GDWoody/Pixel-Controllers/bbb_8_push/jlcpcb/README.md

# BBB 8v1 SMD Push Fit Controller

## Copyright and Disclaimer
Copyright: GDWoody

This documentation describes Open Hardware and is licensed under the CERN Open Hardware License Version 2 - Strongly Reciprocal. (CERN-OHL-S)

You may redistribute and modify this documentation under the terms of the CERN OHL-S-v2 (https://ohwr.org/cern_ohl_s_v2.txt). This documentation is distributed WITHOUT ANY EXPRESS OR IMPLIED WARRANTY, INCLUDING OF MERCHANTABILITY, SATISFACTORY QUALITY AND FITNESS FOR A PARTICULAR PURPOSE. Please see the CERN OHL v2-S for applicable conditions

Under CERN OHL-S-v2, derivative work must be publicly released as defined in subsection 3.3

---
## BBB 8v1 SMD Push Fit Controller PCB's and Part Ordering
Following the instructions below your boards will arrive with only the SMD components fitted. To complete them you will also need to get and fit the 'Additional Components'.  

## To order BBB 8v1 SMD Push Fit PCBs From JLCPCB:

* Download the  [**Gerber_BBB_8v1_SMD_PCB_Push.zip**](https://github.com/GDWoody/Pixel-Controllers/blob/main/bbb_8_push/jlcpcb/gerber/Gerber_BBB_8v1_SMD_PCB_Push.zip) file in the jlcpcb\gerber folder.

* Download the  [**BOM_BBB_8v1_SMD_Push.xlsx**](https://github.com/GDWoody/Pixel-Controllers/blob/main/bbb_8_push/jlcpcb/assembly/BOM_BBB_8v1_SMD_Push.xlsx) file in the jlcpcb\assembly folder.

* Download the  [**CPL_BBB_8v1_SMD_PCB_Push.xlsx**](https://github.com/GDWoody/Pixel-Controllers/blob/main/bbb_8_push/jlcpcb/assembly/CPL_BBB_8v1_SMD_PCB_Push.xlsx) file in the jlcpcb\assembly folder.

*  Goto [**jlcpcb.com**](https://jlcpcb.com), sign in or make a new account, select Instant Quote and Upload the the Gerber_BBB_8v1_SMD_PCB_Push.zip file.

* The default settings should be ok. However you can choose 'PCB Color' and change 'Remove Order Number' to 'Specify a location'.

* Enable the SMD service, 'BOM_BBB_8v1_SMD_Push.xlsx' is the BOM file and 'CPL_BBB_8v1_SMD_PCB_Push.xlsx' is the CPL file.

* [**See here for detailed PCB ordering instructions for JLCPCB**](https://github.com/GDWoody/Pixel-Controllers/blob/main/JLC_PCB.md)

## To order Additional Required Parts from LCSC

* Download the [**BOM_BBB_8v1_SMD_Push_other_parts.xlsx**](https://github.com/GDWoody/Pixel-Controllers/blob/main/bbb_8_push/lcsc/BOM_BBB_8v1_SMD_Push_other_parts.xlsx) file in the lcsc folder.

* Goto [**lcsc.com**](https://lcsc.com), sign in or make a new account and select 'BOM Tool' and upload the BOM_BBB_16v2_SMD_PCB_Other_Parts.xlsx file.

* [**See here for detailed Parts ordering instructions for LCSC**](https://github.com/GDWoody/Pixel-Controllers/blob/main/LCSC.md)

## [**DIY Instructions for a BBB 8v1 SMD Push Fit Controller build**](https://github.com/GDWoody/Pixel-Controllers/blob/main/bbb_8_push/BBB_8v1_Push_DIY.md)

## [**Interactive Bom**](https://gdwoody.github.io/bbb_8_push/BOM_BBB_8v1_SMD_push_ibom.html)

## Additional Components Required

* A BeagleBone Black, BeagleBone Black Wireless, BeagleBone Green, or SanCloud BeagleBone enhanced 

* A SSD1306 128x64 OLED Display
