GDWoody/Pixel-Controllers/bbb_4/image/BBB_4v1_SMD_only.png

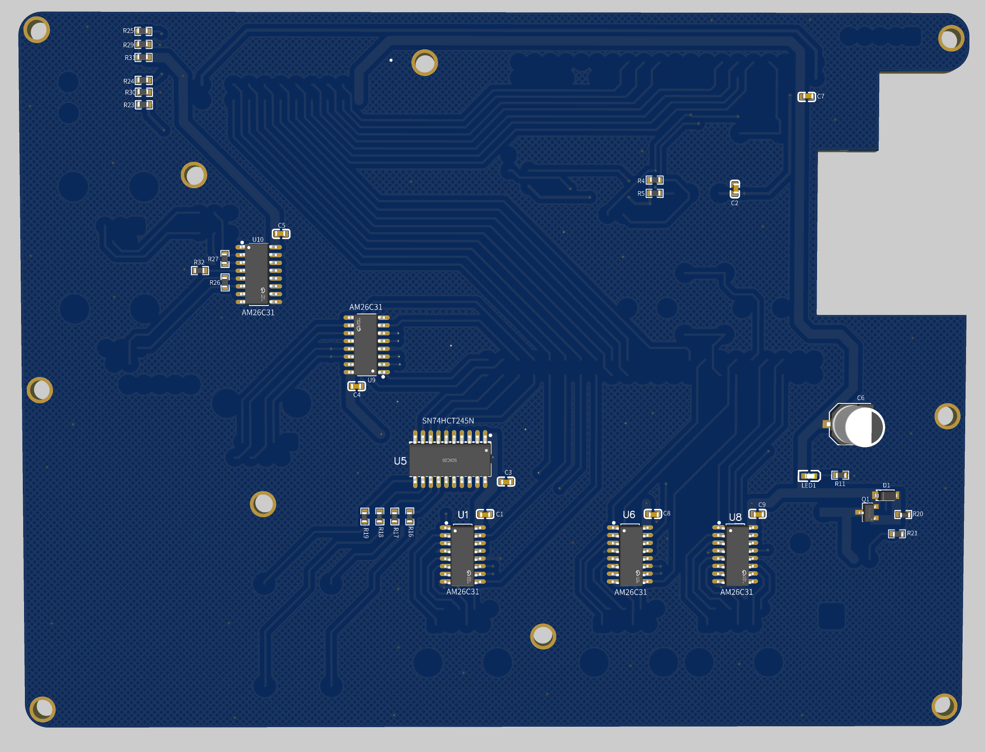
bbb_4/image/BBB_4v1_SMD_only.png
