GDWoody/Pixel-Controllers/bbb_4_push/image/BBB_4v1_Push_SMD_only.png

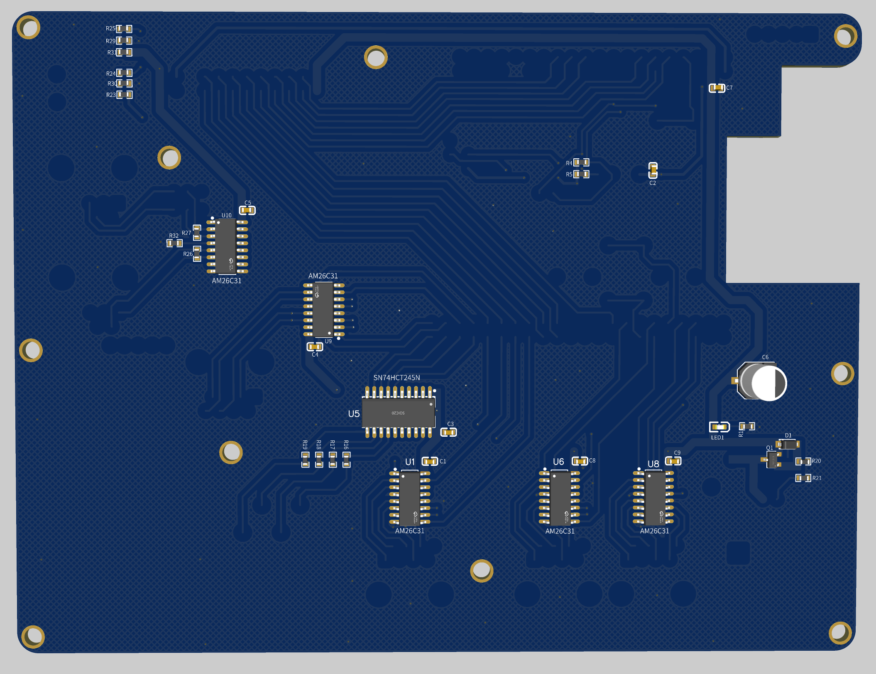
bbb_4_push/image/BBB_4v1_Push_SMD_only.png
