GDWoody/Pixel-Controllers/bbb_8/image/BBB_8v1_no_SMD.png

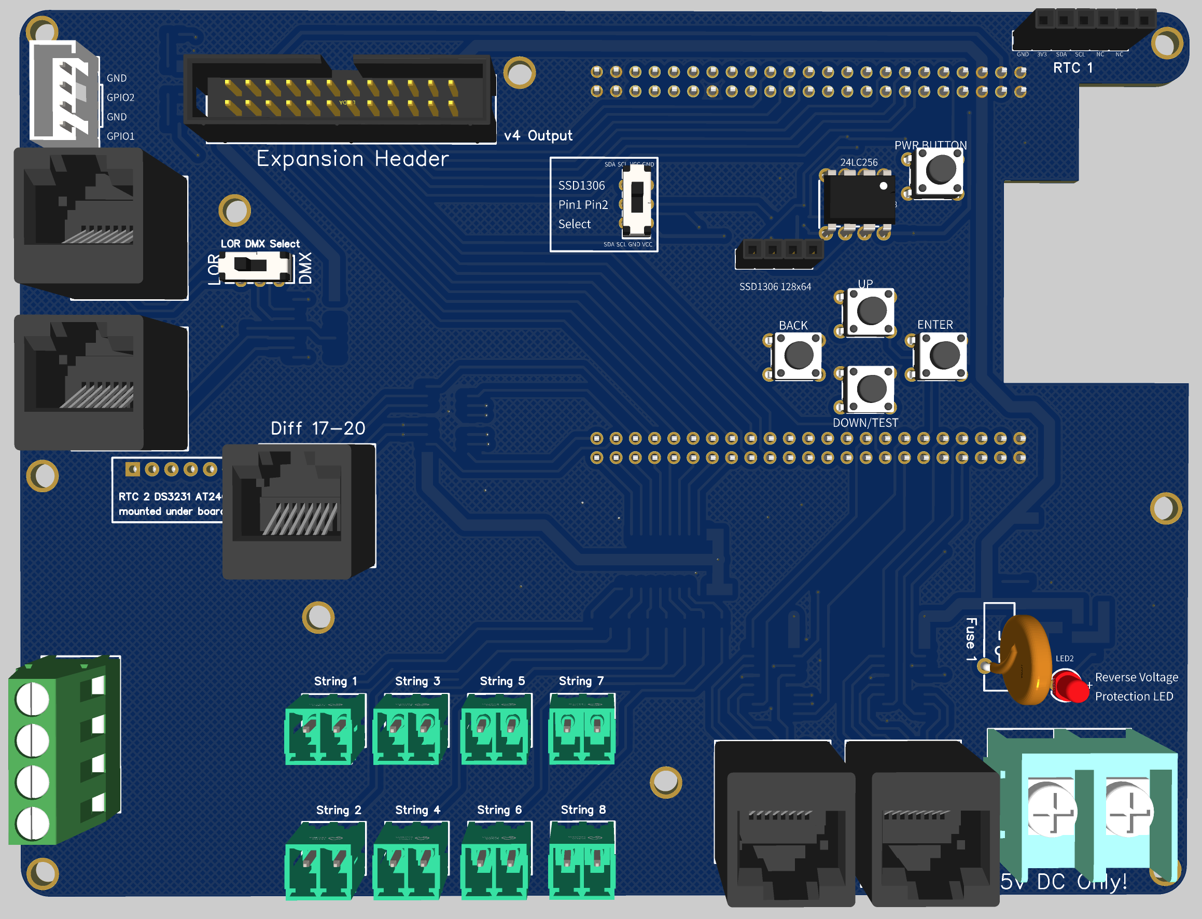
bbb_8/image/BBB_8v1_no_SMD.png
