GDWoody/Pixel-Controllers/bbb_8/image/BBB_8v1_SMD_only.png

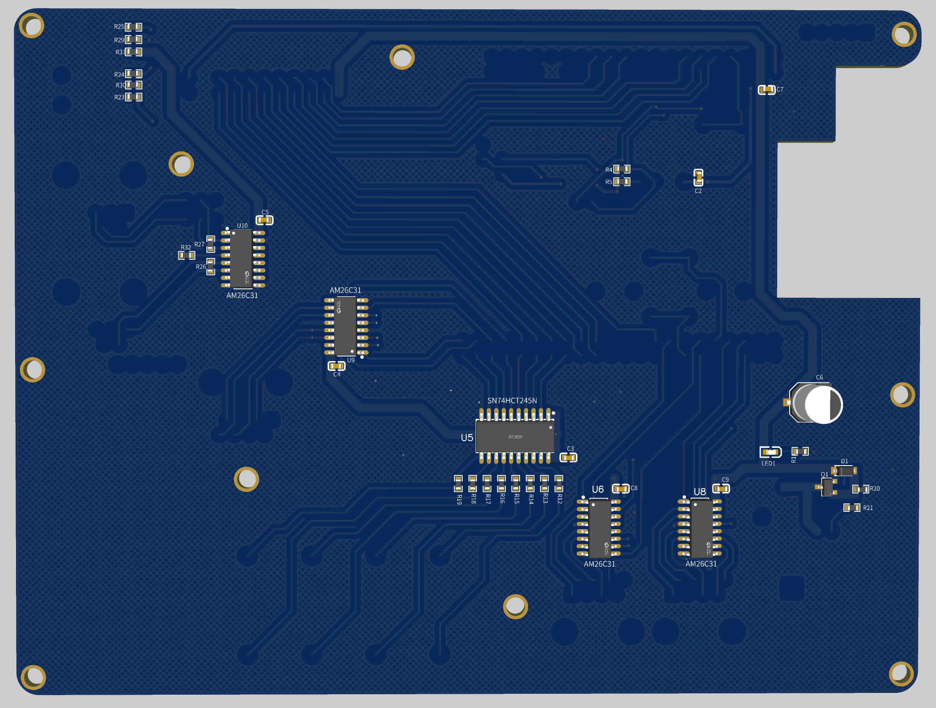
bbb_8/image/BBB_8v1_SMD_only.png
