GDWoody/Pixel-Controllers/bbb_8_push/image/BBB_8v1_Push_Under.png

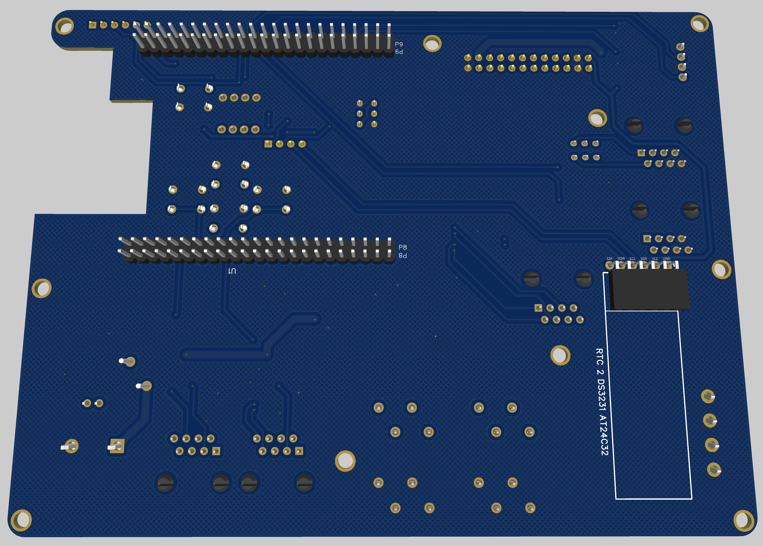
bbb_8_push/image/BBB_8v1_Push_Under.png
