GDWoody/Pixel-Controllers/bbb_16_push/image/BBB_16v2_Push_Other.png

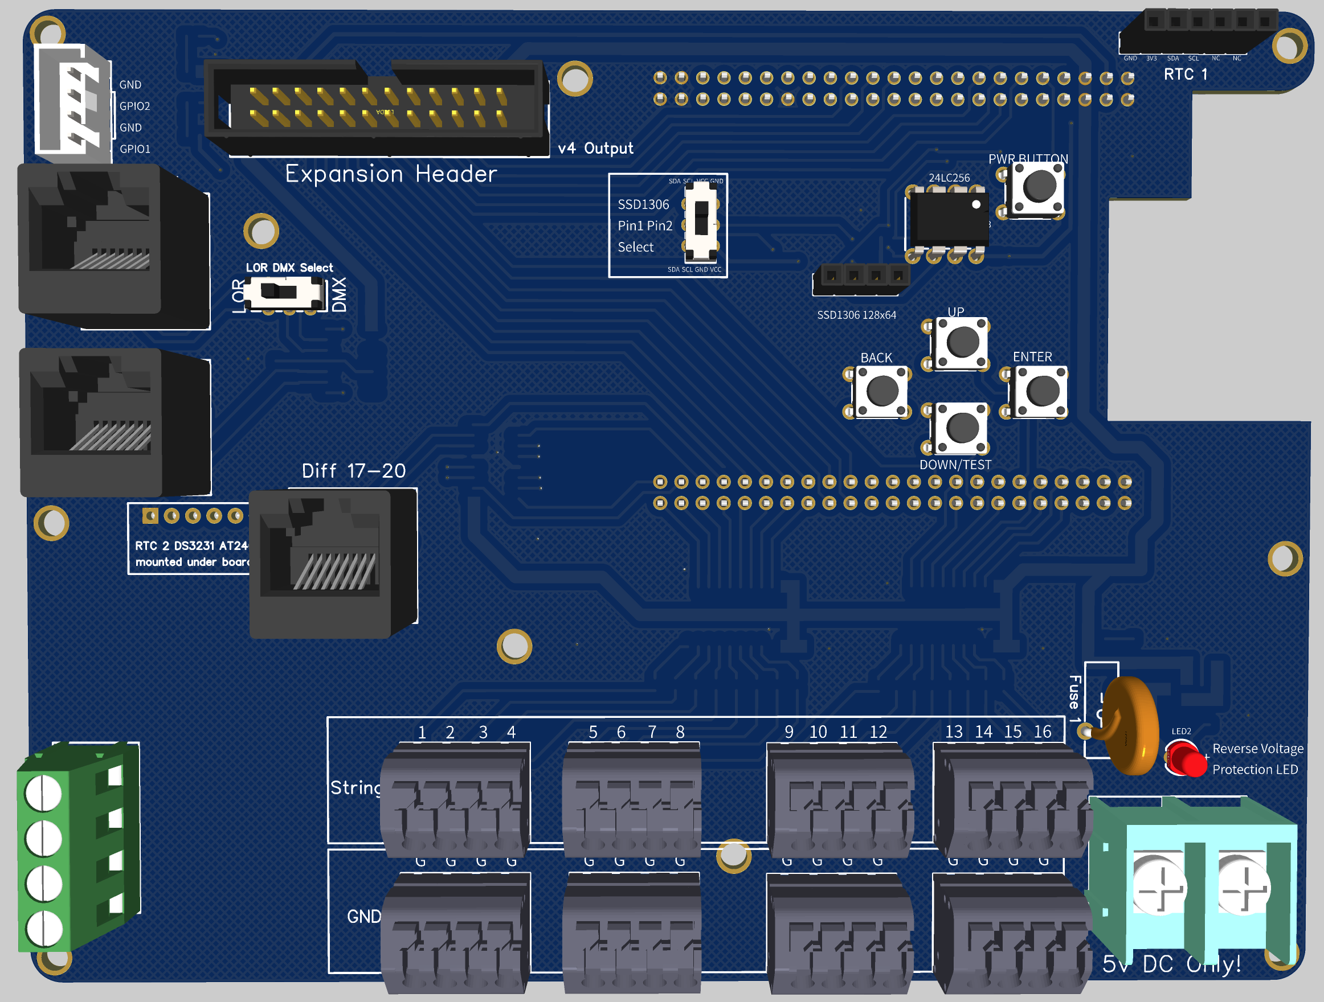
bbb_16_push/image/BBB_16v2_Push_Other.png
