GDWoody/Pixel-Controllers/bbb_16_push/image/BBB_16v2_Push_Under.png

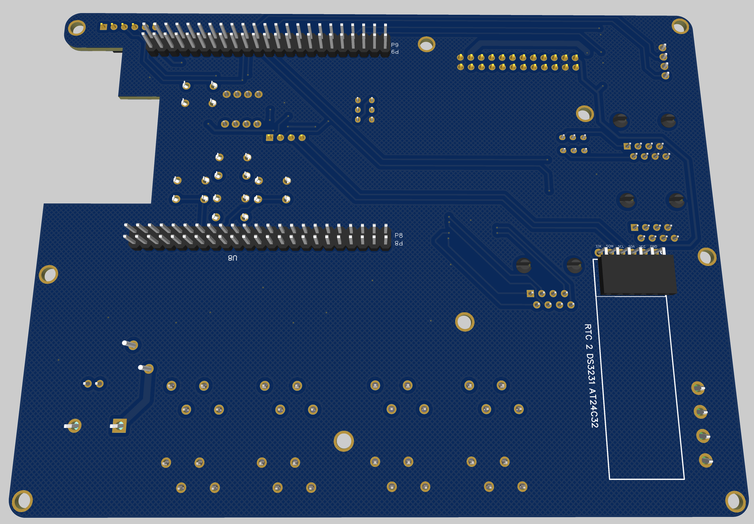
bbb_16_push/image/BBB_16v2_Push_Under.png
