GDWoody/Pixel-Controllers/bbb_all_diff/image/BBB_All_Diff_complete.png

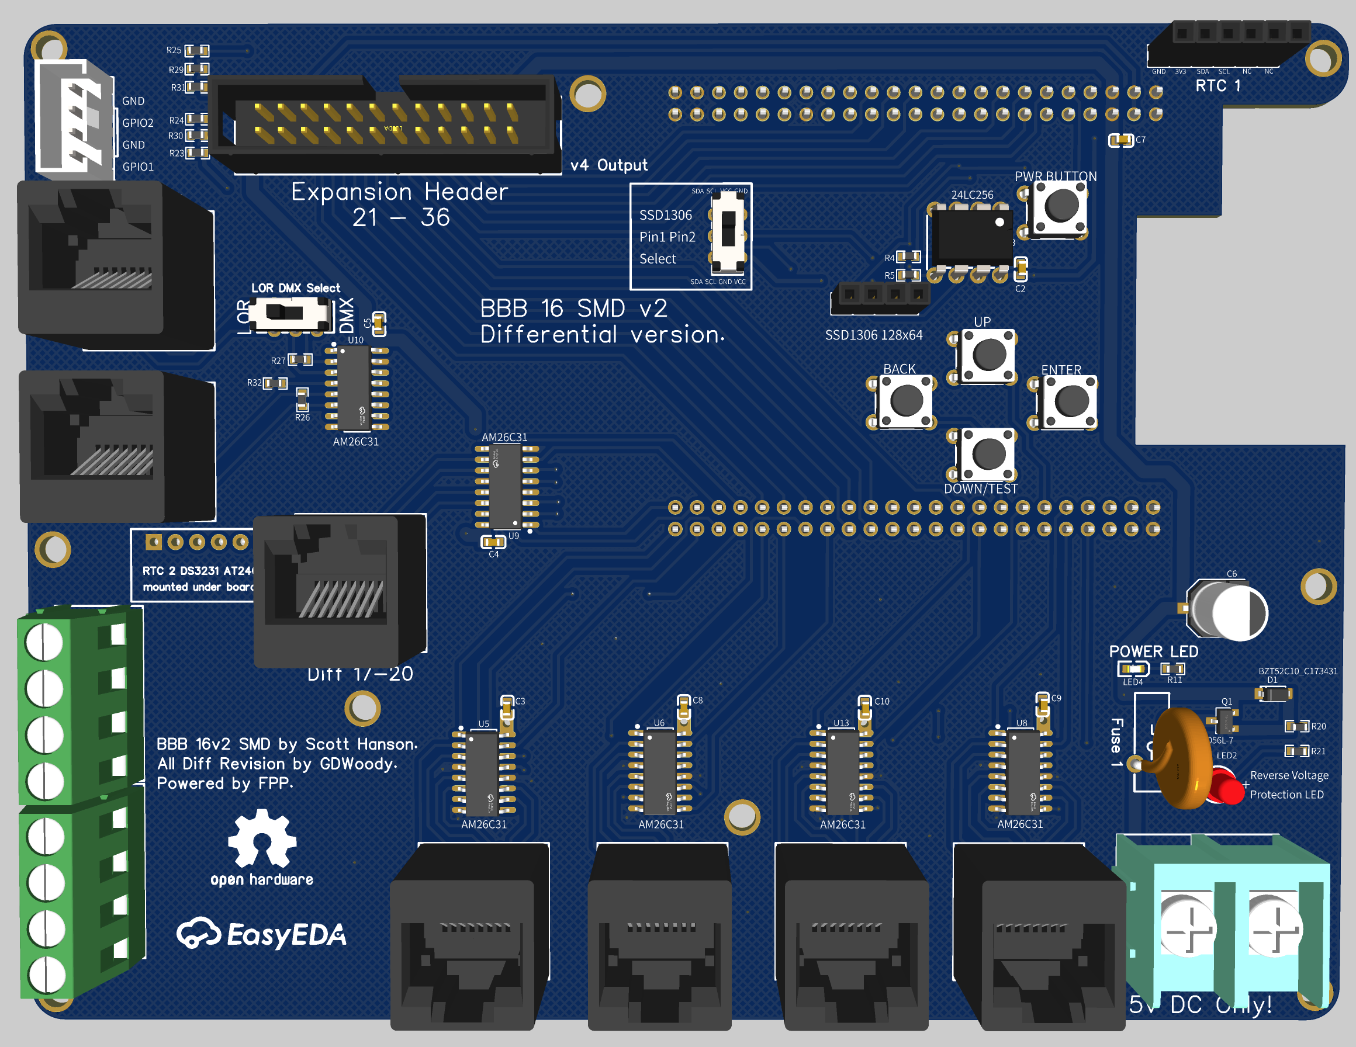
bbb_all_diff/image/BBB_All_Diff_complete.png
