GDWoody/Pixel-Controllers/bbb_all_diff/image/BBB_All_Diff_no_SMD.png

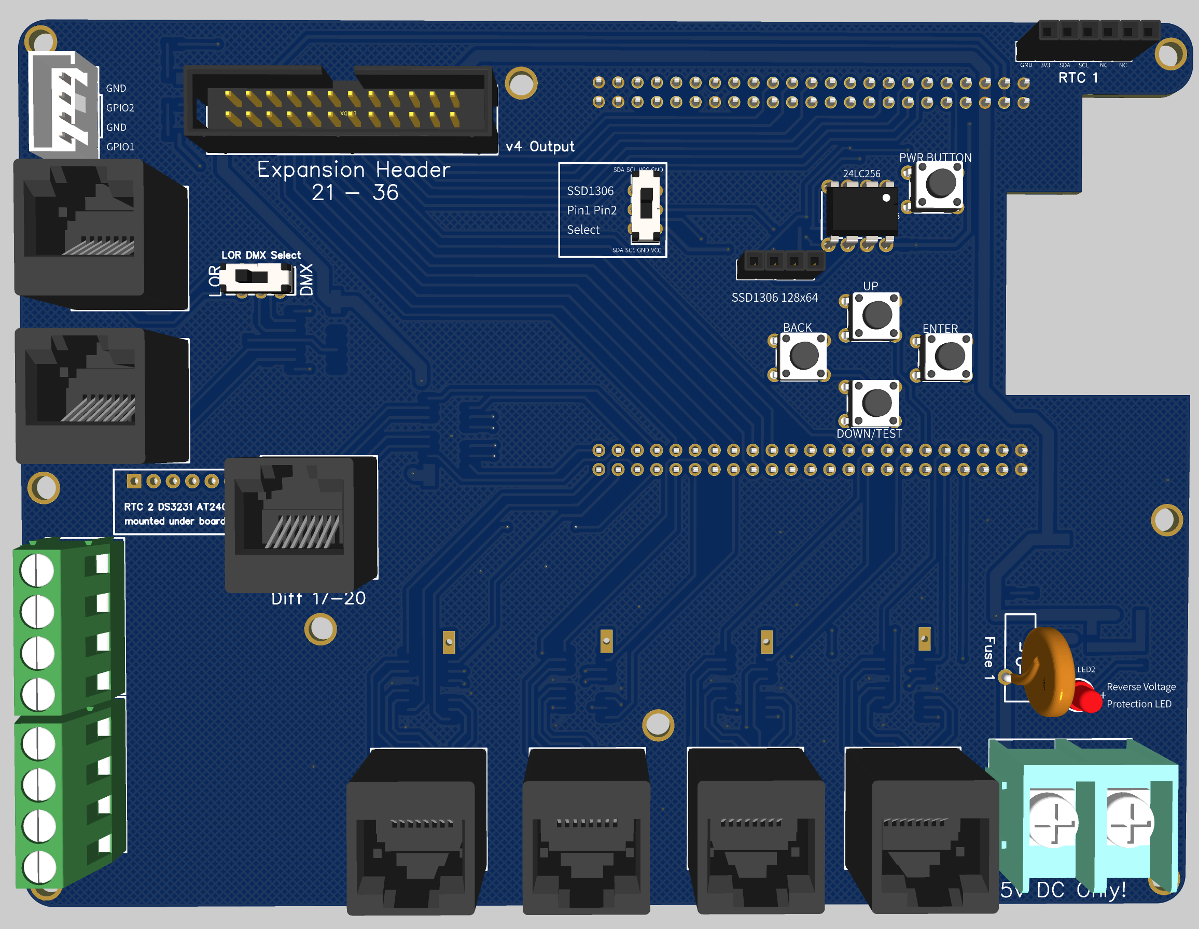
bbb_all_diff/image/BBB_All_Diff_no_SMD.png
