GDWoody/Pixel-Controllers/bbb_all_diff/image/BBB_All_Diff_SMD_only.png

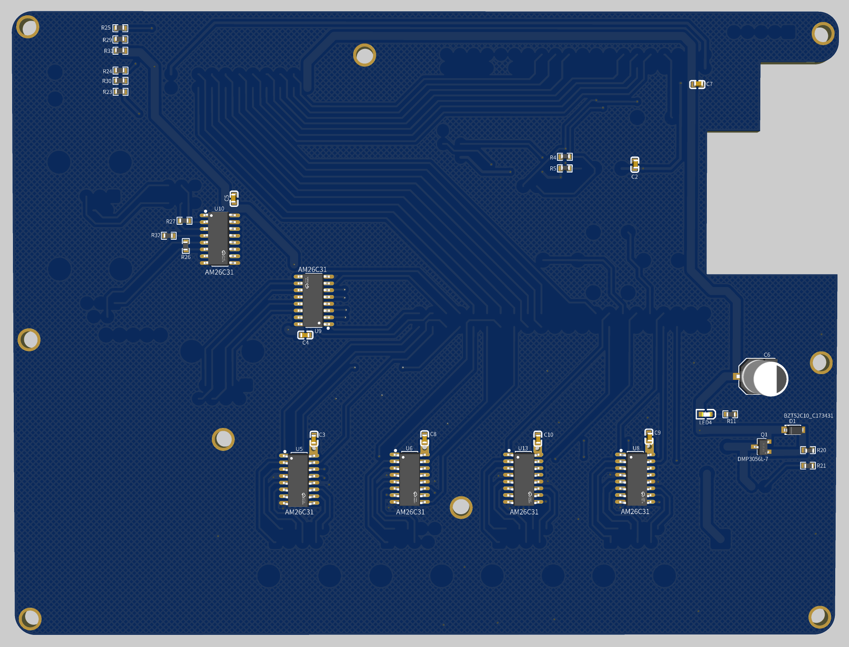
bbb_all_diff/image/BBB_All_Diff_SMD_only.png
