GDWoody/Pixel-Controllers/bbb_diff_expansion/jlcpcb/assembly/BOM_Diff_Expansion_SMD.xlsx

Name | Designator | Footprint | Quantity | Manufacturer Part | Supplier | Supplier Part
KT-0603R | LED2 | LED0603-RD | 1 | KT-0603R | LCSC | C2286
680 | R13 | R0603 | 1 | 0603WAF6800T5E | LCSC | C23228
100nF | C2,C7,C4,C1 | C0603 | 4 | CC0603KRX7R9BB104 | LCSC | C14663
AM26C31IDR | U2,U4,U5,U1 | SOIC-16_L9.9-W3.9-P1.27-LS6.0-BL | 4 | AM26C31IDR | LCSC | C34923
