GDWoody/Pixel-Controllers/bbb_16_expansion/jlcpcb/assembly/BOM_16_Expansion_SMD.xlsx

Name | Designator | Footprint | Quantity | Manufacturer Part | Supplier | Supplier Part
100nF | C1,C3 | C0603 | 2 | CC0603KRX7R9BB104 | LCSC | C14663
KT-0603R | LED2 | LED0603-RD | 1 | KT-0603R | LCSC | C2286
100Ω | R1,R2,R3,R4,R5,R6,R7,R8,R9,R10,R11,R12,R13,R14,R15,R16 | R0603 | 16 | 0603WAF1000T5E | LCSC | C22775
10kΩ | R17,R18,R19,R20,R21,R22,R23,R24,R25,R26,R27,R28,R29,R30,R31,R32 | R0603 | 16 | 0603WAF1002T5E | LCSC | C25804
33 | R33,R34,R35,R36,R37,R38,R39,R40,R41,R42,R43,R44,R45,R46,R47,R48 | R0603 | 16 | 0603WAF330JT5E | LCSC | C23140
680 | R49 | R0603 | 1 | 0603WAF6800T5E | LCSC | C23228
SN74HCT245NSR | U5,U1 | SOIC-20_L13.3-W5.5-P1.27-LS7.8-BL | 2 | SN74HCT245NSR | LCSC | C133641
