GDWoody/Pixel-Controllers/diff_receiver_v3/Schematic_Differentcial_Receiver_v3.pdf

# Receiver

+5V

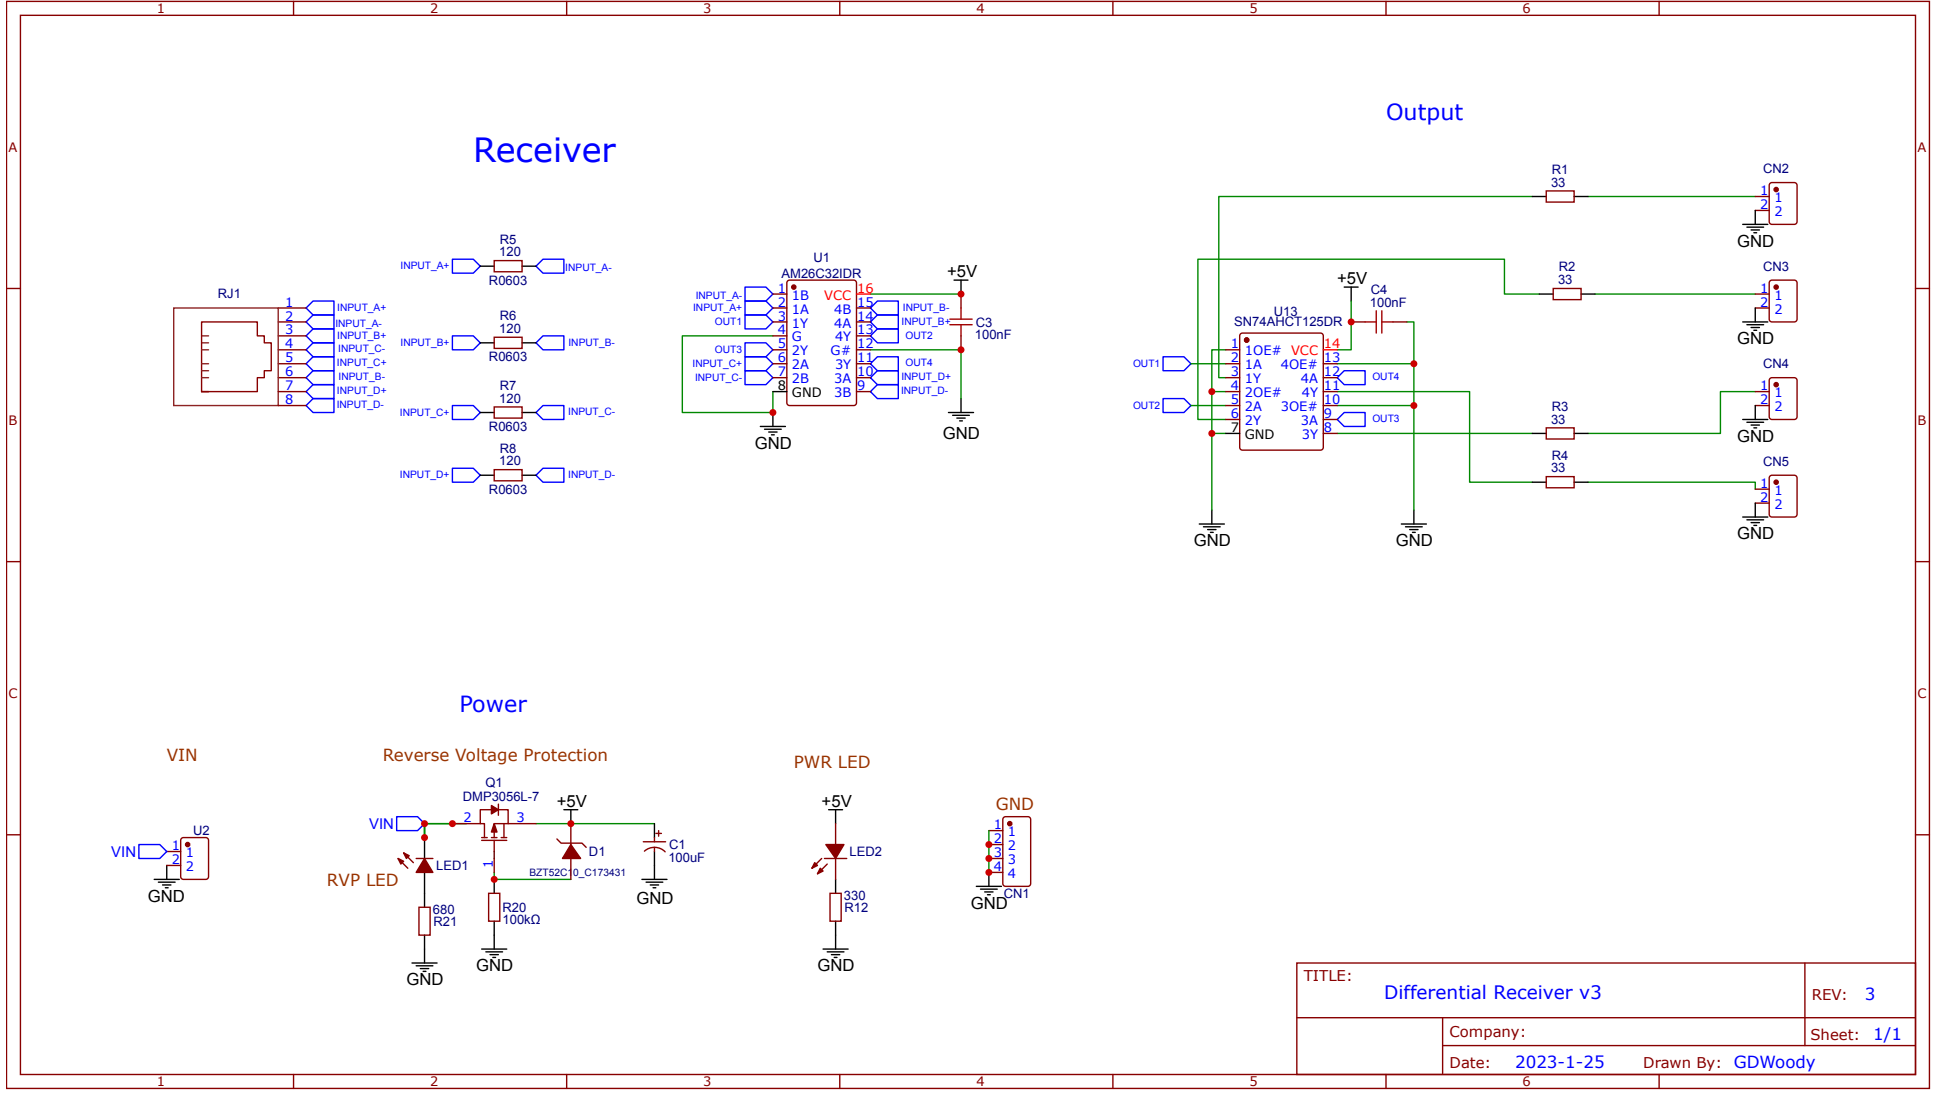
[picture p106: page 1]
